maxbundscherer/independer-loras/case/howexport.png

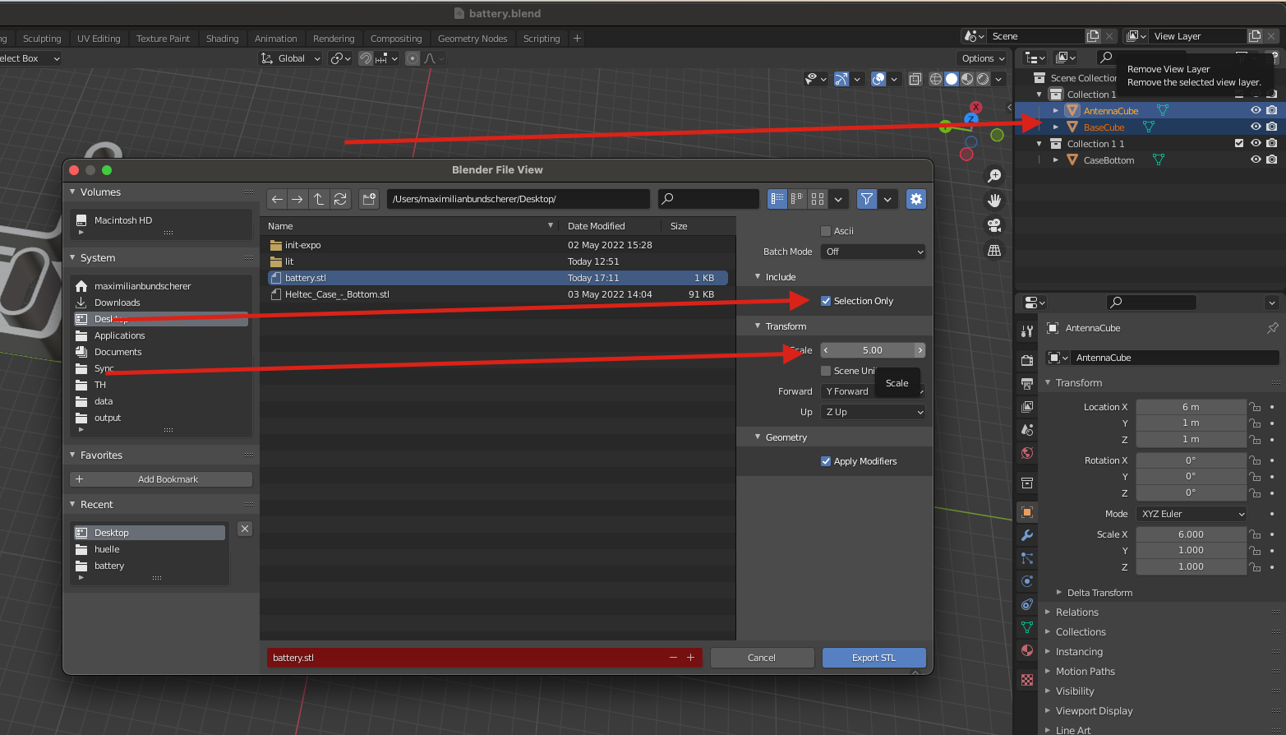
case/howexport.png
