maxbundscherer/independer-loras/case/howimport.png

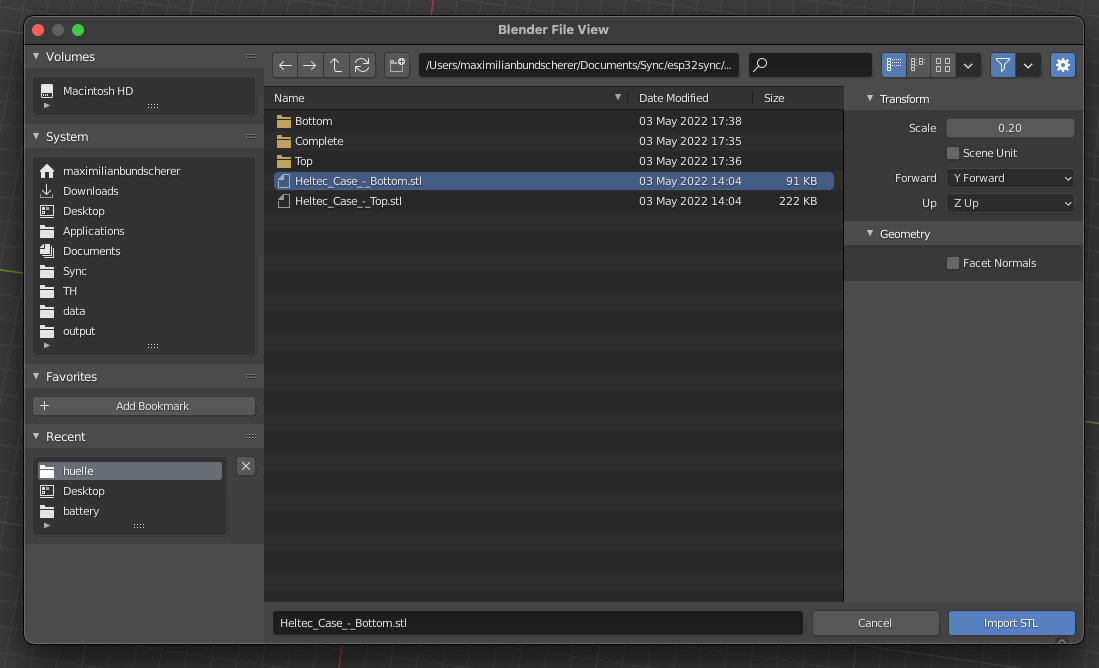
case/howimport.png
